Vasil-Pahomov/Arduino-THS/Data.h

#ifndef Data_h
#define Data_h

//defines data entry
//yes I know using static structure is not flexible, but it much simplier to handle
typedef struct Data {

  //temperature, in Celsius multiplied by 100
  int16_t temp;

  //relative humidity, in percent multiplied by 100
   uint16_t hum;

   //CO2, in ppm
   uint16_t co2;
   
   //PM1.0 reading, in ug/m^3
   uint16_t pm1;

   //PM2.5 reading, in ug/m^3
   uint16_t pm25;

   //PM10 reading, in ug/m^3
   uint16_t pm10;

   //TVOC reading, ppd
   uint16_t tvoc;
   
} Data;

#endif
